347800570/stm32-led-gift/Software/Official Version/MPLT_V03/Core/Src/led_layout.c

#include "led_layout.h"
#if LED_COUNT != 67U
#error Update the physical layout when changing LED_COUNT
#endif

/* 来自用户确认的灯带位置.txt，保留第一个字的高度差和第四个字的不对称。 */
const LED_Position led_positions[LED_COUNT] = {
    /* 1..24：第一个字 */
    {0,1},{0,2},{0,3},{0,4},{0,5},{0,6},{0,7},
    {1,7},{2,7},{3,7},{4,7},{5,7},
    {3,6},{3,5},{3,4},{3,3},{3,2},{3,1},
    {5,1},{5,2},{5,3},{5,4},{5,5},{5,6},
    /* 25..42：第二个字 */
    {8,7},{8,6},{8,5},{8,4},{8,3},{8,2},{8,1},{8,0},
    {9,4},{10,4},{11,4},{12,4},{12,5},{12,6},
    {9,7},{10,7},{11,7},{12,7},
    /* 43..54：第三个字 */
    {15,7},{15,6},{15,5},{15,4},{15,3},{15,2},{15,1},{15,0},
    {16,0},{17,0},{18,0},{19,0},
    /* 55..67：第四个字，竖线在 x=23，与 65 号对齐 */
    {23,0},{23,1},{23,2},{23,3},{23,4},{23,5},{23,6},
    {26,7},{25,7},{24,7},{23,7},{22,7},{21,7}
};
