347800570/stm32-led-gift/Software/Official Version/SRKL_V01/Core/Src/led_layout.c

#include "led_layout.h"
#if LED_COUNT != 74U
#error Update the physical layout when changing LED_COUNT
#endif

/* 按灯带位置.txt的制表符列和行映射；y=0为最底部，保留内部空隙。 */
const LED_Position led_positions[LED_COUNT] = {
    {5,0}, /* 1 */
    {3,0}, /* 2 */
    {1,0}, /* 3 */
    {1,4}, /* 4 */
    {3,4}, /* 5 */
    {5,4}, /* 6 */
    {5,7}, /* 7 */
    {3,7}, /* 8 */
    {1,7}, /* 9 */
    {0,5}, /* 10 */
    {0,7}, /* 11 */
    {0,9}, /* 12 */
    {3,9}, /* 13 */
    {3,6}, /* 14 */
    {3,5}, /* 15 */
    {3,3}, /* 16 */
    {3,2}, /* 17 */
    {3,1}, /* 18 */
    {9,1}, /* 19 */
    {9,3}, /* 20 */
    {9,5}, /* 21 */
    {9,7}, /* 22 */
    {10,8}, /* 23 */
    {12,8}, /* 24 */
    {14,8}, /* 25 */
    {15,7}, /* 26 */
    {15,5}, /* 27 */
    {15,3}, /* 28 */
    {15,1}, /* 29 */
    {14,0}, /* 30 */
    {12,0}, /* 31 */
    {10,0}, /* 32 */
    {10,4}, /* 33 */
    {12,4}, /* 34 */
    {14,4}, /* 35 */
    {17,4}, /* 36 */
    {18,5}, /* 37 */
    {19,11}, /* 38 */
    {19,9}, /* 39 */
    {19,7}, /* 40 */
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
};
