347800570/stm32-led-gift/Software/Test/3_Light Led/Core/Src/main.c

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
/* Includes ------------------------------------------------------------------*/
#include "main.h"
#include "dma.h"
#include "tim.h"
#include "usart.h"
#include "usb.h"
#include "gpio.h"

/* USER CODE BEGIN PD */
#define WS2812_LED_COUNT          10U
#define WS2812_BITS_PER_LED       24U
#define WS2812_RESET_SLOTS        64U
#define WS2812_BUFFER_SIZE        ((WS2812_LED_COUNT * WS2812_BITS_PER_LED) + WS2812_RESET_SLOTS)

/* TIM3 runs at 48 MHz with ARR=59: 19 ticks encode 0, 38 ticks encode 1. */
#define WS2812_DUTY_0             19U
#define WS2812_DUTY_1             38U
#define WS2812_DMA_TIMEOUT_MS     100U
#define WS2812_TEST_BRIGHTNESS    16U
/* USER CODE END PD */


/* USER CODE BEGIN PV */
static uint16_t ws2812_pwm_buffer[WS2812_BUFFER_SIZE];
static volatile uint8_t ws2812_dma_complete;
/* USER CODE END PV */

void SystemClock_Config(void);
/* USER CODE BEGIN PFP */
static void WS2812_FillSolidColor(uint8_t red, uint8_t green, uint8_t blue);
static HAL_StatusTypeDef WS2812_Send(uint32_t channel);
/* USER CODE END PFP */

/* USER CODE BEGIN 0 */

/**
  * @brief Convert one solid RGB color into a WS2812B PWM duty-cycle stream.
  * @note  WS2812B expects each pixel in GRB order, most-significant bit first.
  */
static void WS2812_FillSolidColor(uint8_t red, uint8_t green, uint8_t blue)
{
  uint32_t color = ((uint32_t)green << 16U) |
                   ((uint32_t)red << 8U) |
                   (uint32_t)blue;
  uint32_t index = 0U;

  for (uint32_t led = 0U; led < WS2812_LED_COUNT; led++)
  {
    for (uint32_t bit = 0U; bit < WS2812_BITS_PER_LED; bit++)
    {
      uint32_t mask = 1UL << (23U - bit);
      ws2812_pwm_buffer[index++] = ((color & mask) != 0U) ?
                                    WS2812_DUTY_1 : WS2812_DUTY_0;
    }
  }

  /* A low level longer than 50 us makes the LEDs latch the received color. */
  while (index < WS2812_BUFFER_SIZE)
  {
    ws2812_pwm_buffer[index++] = 0U;
  }
}

/**
  * @brief Send the prepared PWM stream through one TIM3 channel.
  */
static HAL_StatusTypeDef WS2812_Send(uint32_t channel)
{
  HAL_StatusTypeDef status;
  uint32_t start_tick;

  ws2812_dma_complete = 0U;
  __HAL_TIM_SET_COMPARE(&htim3, channel, 0U);
  __HAL_TIM_SET_COUNTER(&htim3, 0U);

  status = HAL_TIM_PWM_Start_DMA(&htim3,
                                 channel,
                                 (const uint32_t *)ws2812_pwm_buffer,
                                 (uint16_t)WS2812_BUFFER_SIZE);
  if (status != HAL_OK)
  {
    return status;
  }

  start_tick = HAL_GetTick();
  while (ws2812_dma_complete == 0U)
  {
    if ((HAL_GetTick() - start_tick) >= WS2812_DMA_TIMEOUT_MS)
    {
      (void)HAL_TIM_PWM_Stop_DMA(&htim3, channel);
      __HAL_TIM_SET_COMPARE(&htim3, channel, 0U);
      return HAL_TIMEOUT;
    }
  }

  (void)HAL_TIM_PWM_Stop_DMA(&htim3, channel);
  __HAL_TIM_SET_COMPARE(&htim3, channel, 0U);
  return HAL_OK;
}

/* USER CODE END 0 */

/**
  * @brief  The application entry point.
  * @retval int
  */
int main(void)
{

  /* MCU Configuration--------------------------------------------------------*/

  /* Reset of all peripherals, Initializes the Flash interface and the Systick. */
  HAL_Init();

  /* Configure the system clock */
  SystemClock_Config();

  /* Initialize all configured peripherals */
  MX_GPIO_Init();
  MX_DMA_Init();
  MX_TIM1_Init();
  MX_USART1_UART_Init();
  MX_USB_PCD_Init();
  MX_TIM3_Init();
  /* USER CODE BEGIN 2 */

  /* Allow the 5 V LED supply and the level shifter to become stable. */
  HAL_Delay(100U);

  /* LED1_DATA on PB0/TIM3_CH3: ten low-brightness red pixels. */
  WS2812_FillSolidColor(WS2812_TEST_BRIGHTNESS, 0U, 0U);
  if (WS2812_Send(TIM_CHANNEL_3) != HAL_OK)
  {
    Error_Handler();
  }

  /* LED2_DATA on PB1/TIM3_CH4: ten low-brightness green pixels. */
  WS2812_FillSolidColor(0U, WS2812_TEST_BRIGHTNESS, 0U);
  if (WS2812_Send(TIM_CHANNEL_4) != HAL_OK)
  {
    Error_Handler();
  }

  /* USER CODE END 2 */

  /* Infinite loop */
  /* USER CODE BEGIN WHILE */
  while (1)
  {
    /* USER CODE END WHILE */

    /* USER CODE BEGIN 3 */
  }
  /* USER CODE END 3 */
}

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
/* USER CODE BEGIN 4 */

/**
  * @brief Called by the HAL after one TIM PWM DMA transfer finishes.
  */
void HAL_TIM_PWM_PulseFinishedCallback(TIM_HandleTypeDef *htim)
{
  if (htim->Instance == TIM3)
  {
    ws2812_dma_complete = 1U;
  }
}

/* USER CODE END 4 */
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
